fleshgordo/diskohedronled/pcb/screenshots/topmounting_revF.png

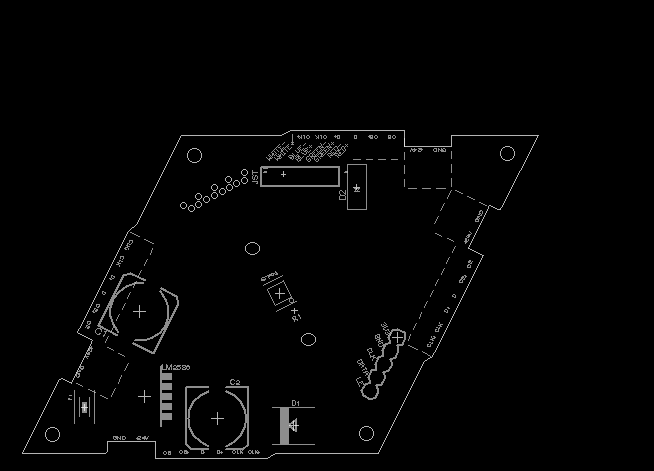
pcb/screenshots/topmounting_revF.png
