fleshgordo/diskohedronled/pcb/partlist/MountingBottomrevb.png

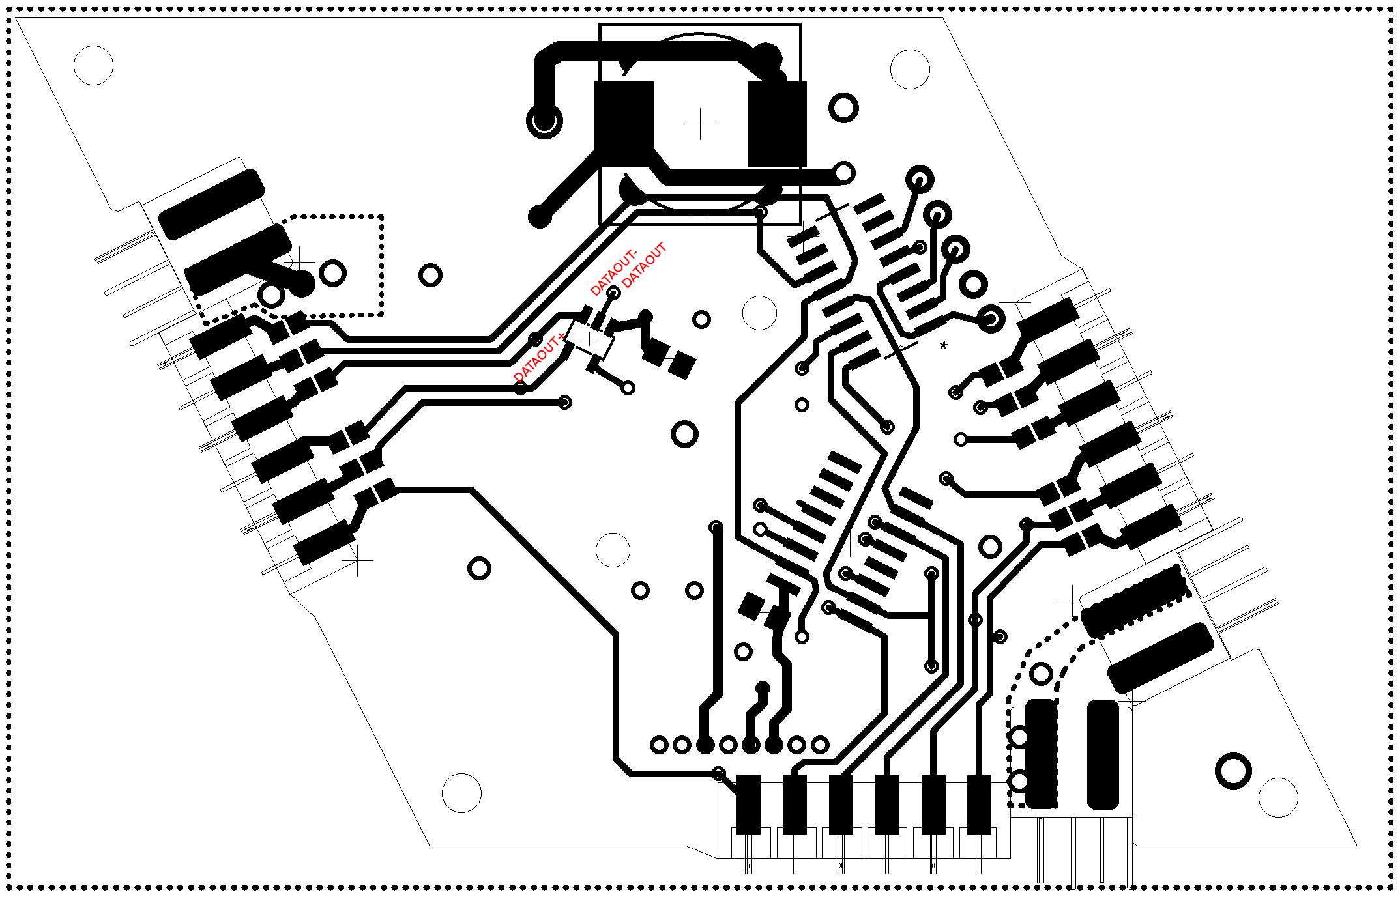
pcb/partlist/MountingBottomrevb.png
