fleshgordo/diskohedronled/pcb/partlist/MountingToprevc.png

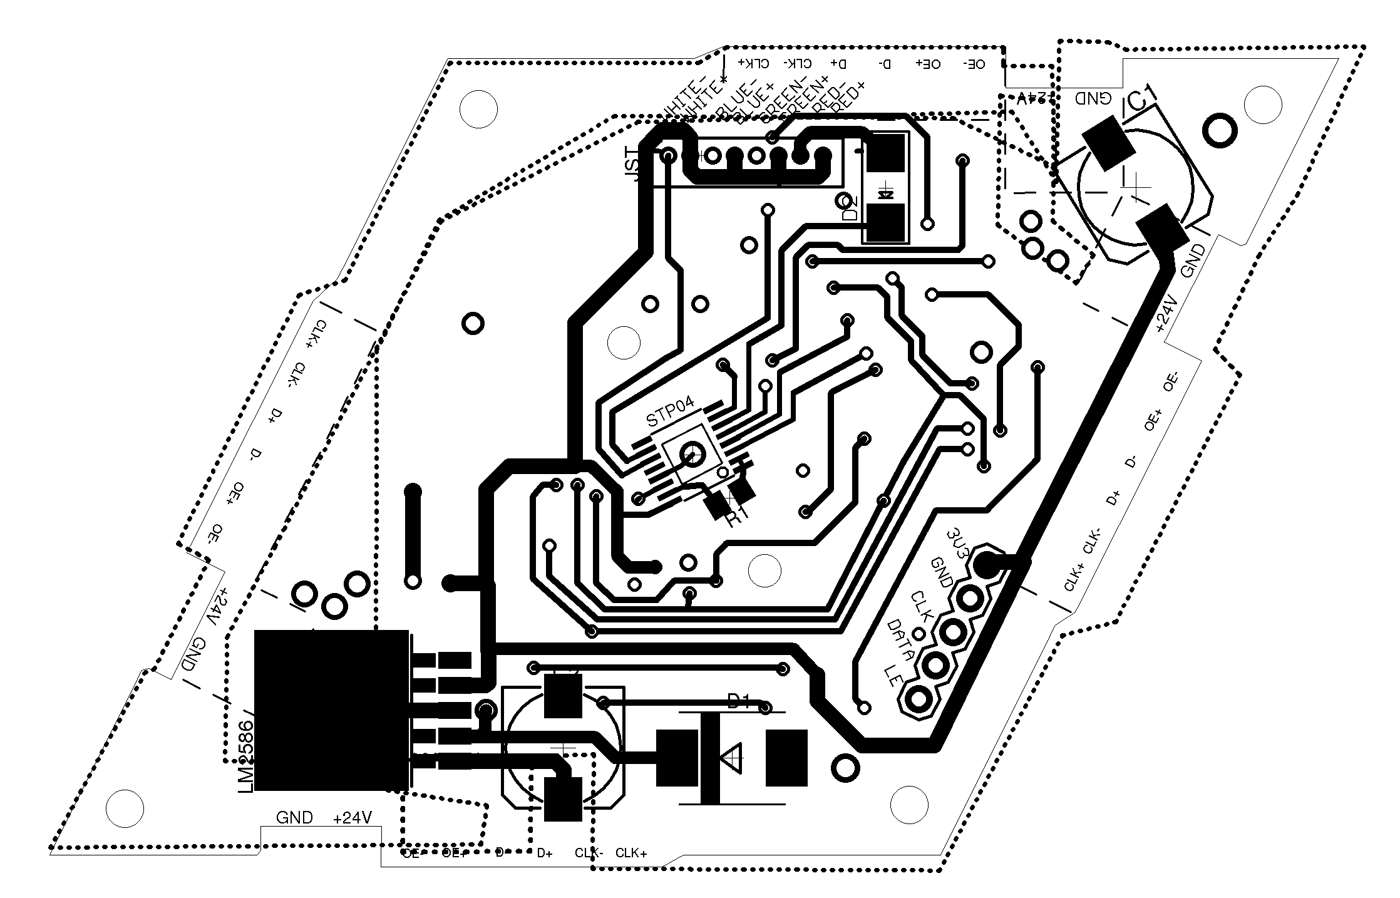
pcb/partlist/MountingToprevc.png
