fleshgordo/diskohedronled/construction/3dmodel/powerunit-box-revF.stl

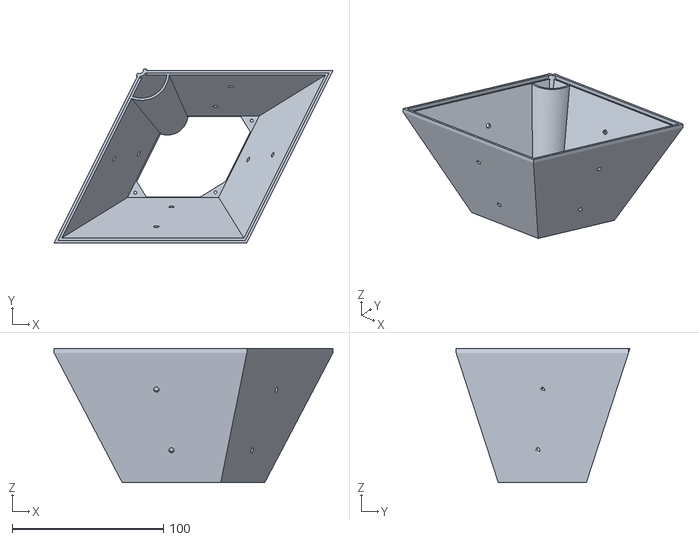
[picture p23: CAD file, 2015-05-11]
construction/3dmodel/powerunit-box-revF.stl
184.4 x 114.8 x 88.9
