fleshgordo/diskohedronled/construction/3dmodel/powerunit-triangle-revF-3rupe.stl

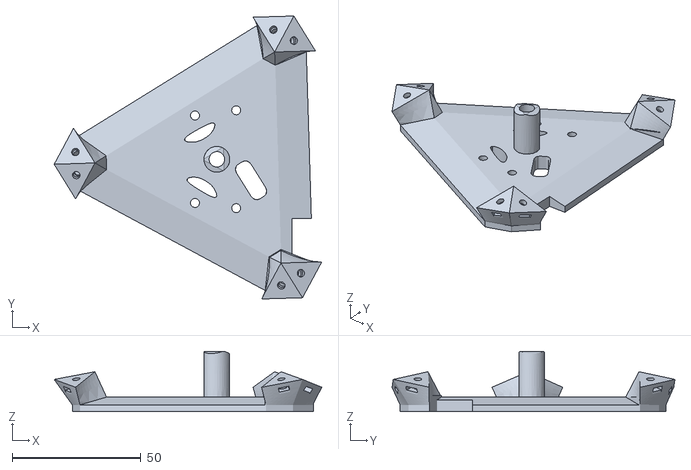
[picture p24: CAD file, 2015-05-11]
construction/3dmodel/powerunit-triangle-revF-3rupe.stl
104.0 x 109.9 x 23.5
