fleshgordo/diskohedronled/construction/3dmodel/powerunit-L-revF.stl

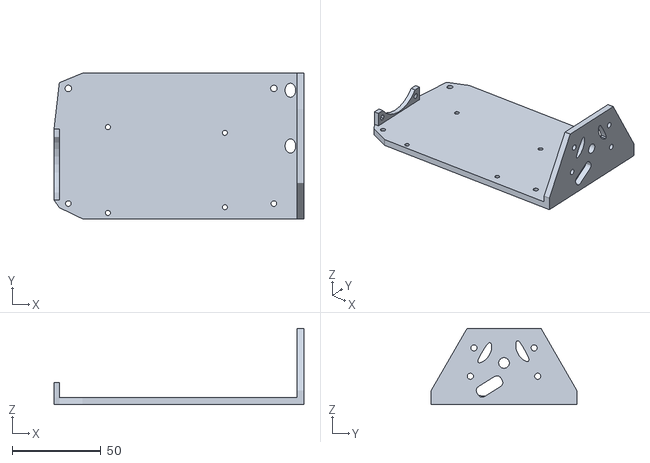
[picture p25: CAD file, 2015-05-11]
construction/3dmodel/powerunit-L-revF.stl
141.1 x 82.2 x 43.0
