fleshgordo/diskohedronled/construction/3dmodel/TeensyHolder108.stl

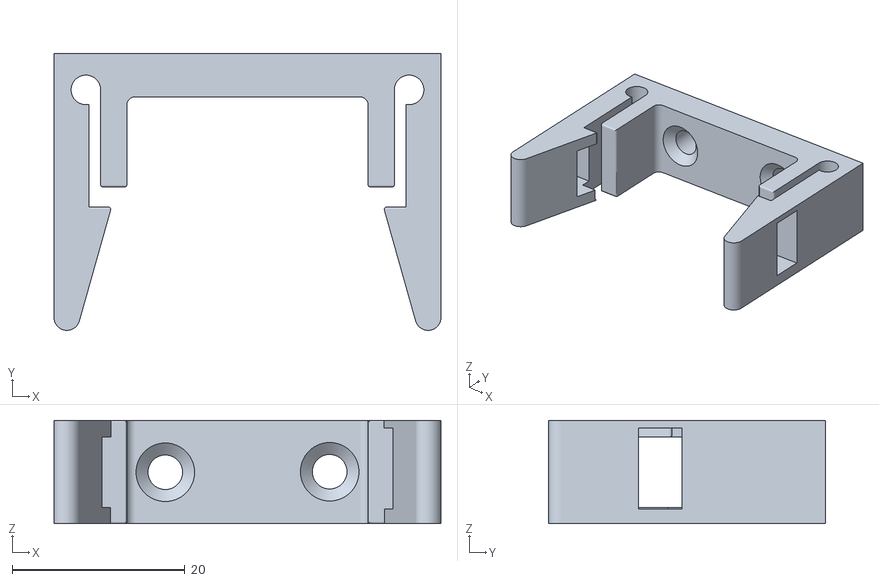
[picture p26: CAD file, 2015-05-11]
construction/3dmodel/TeensyHolder108.stl
44.9 x 32.1 x 12.0
