fleshgordo/diskohedronled/construction/3dmodel/piramida-revF-1-6-mesh.stl

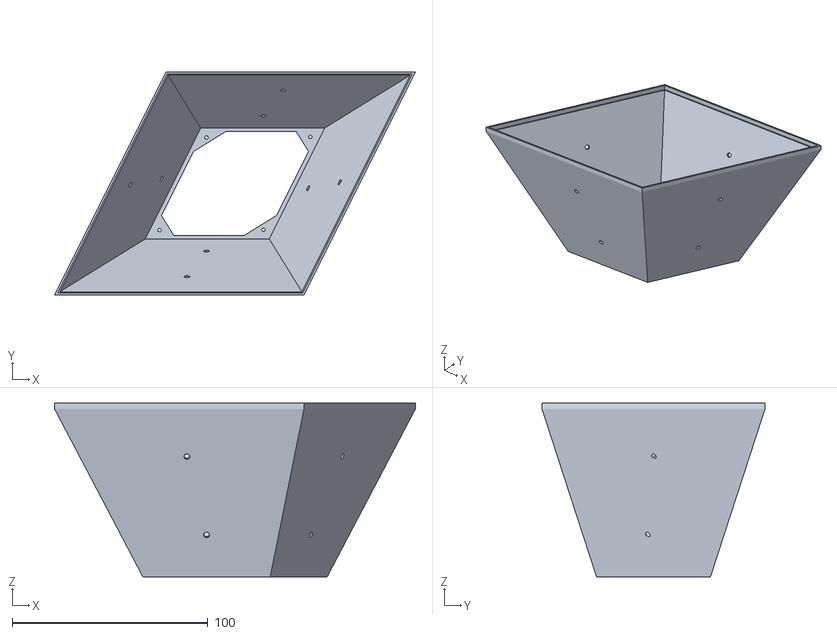
[picture p27: CAD file, 2015-03-30]
construction/3dmodel/piramida-revF-1-6-mesh.stl
184.4 x 113.9 x 88.9
