fleshgordo/diskohedronled/construction/3dmodel/piramida-revF.stl

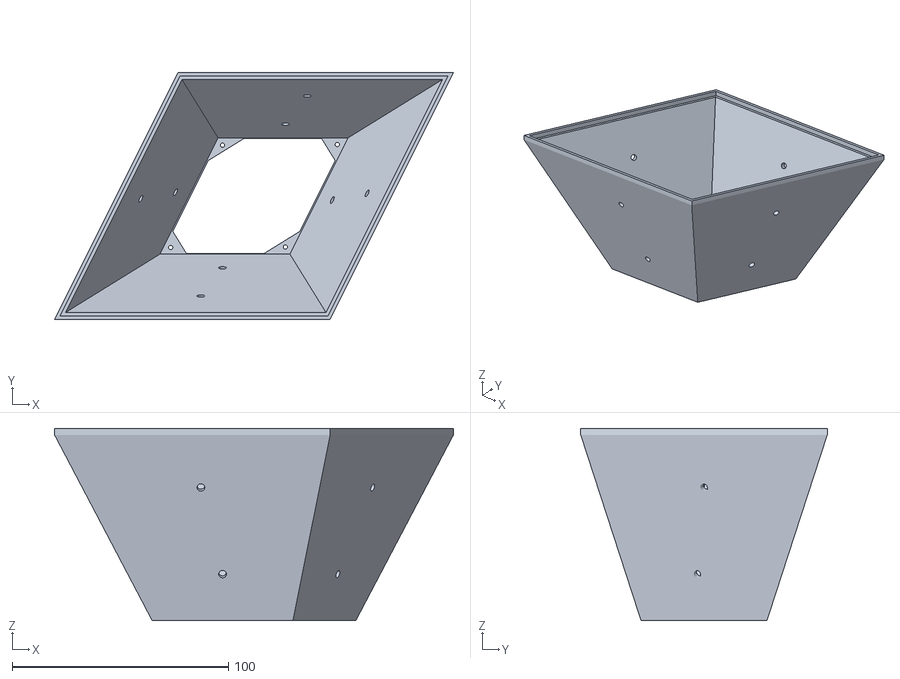
[picture p28: CAD file, 2015-03-30]
construction/3dmodel/piramida-revF.stl
184.4 x 113.9 x 88.9
