fleshgordo/diskohedronled/construction/3dmodel/powerunit-L-revB-3Dutility.stl

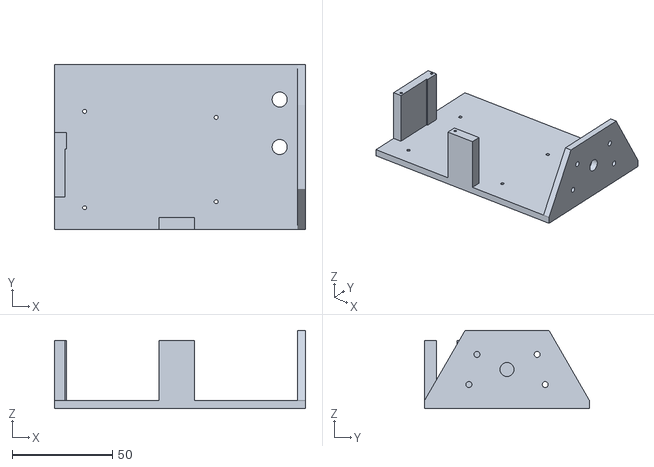
[picture p29: CAD file, 2015-03-28]
construction/3dmodel/powerunit-L-revB-3Dutility.stl
125.0 x 82.2 x 39.0
