fleshgordo/diskohedronled/construction/3dmodel/powerunit-triangle-revB-3Dutility.stl

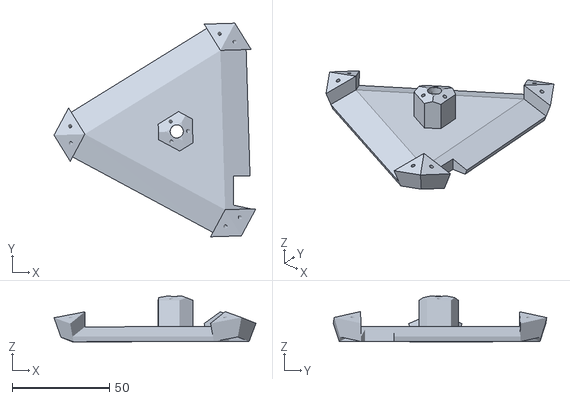
[picture p30: CAD file, 2015-03-28]
construction/3dmodel/powerunit-triangle-revB-3Dutility.stl
104.0 x 110.0 x 23.5
