fleshgordo/diskohedronled/construction/3dmodel/piramida-revB-2boxes-3Dutility.stl

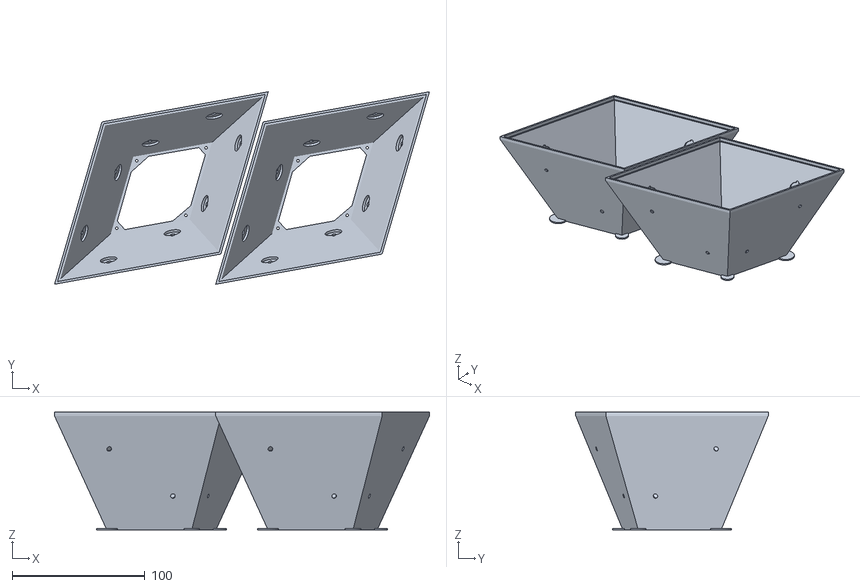
[picture p31: CAD file, 2014-12-30]
construction/3dmodel/piramida-revB-2boxes-3Dutility.stl
282.5 x 145.1 x 88.8
