fleshgordo/diskohedronled/construction/3dmodel/piramida-revB-3dutility.stl

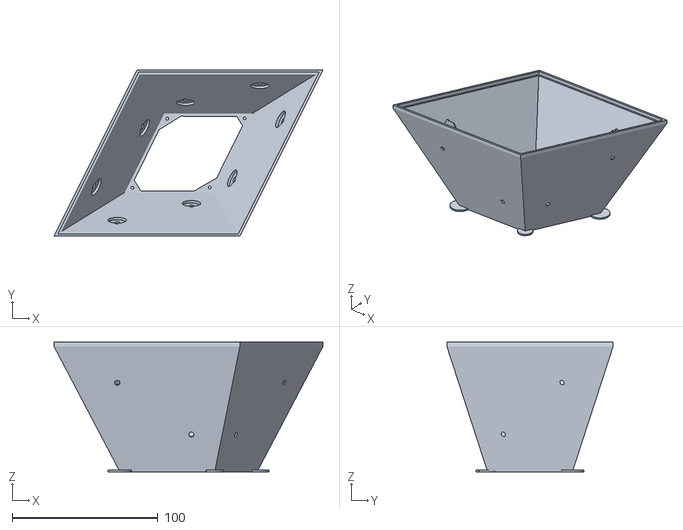
[picture p32: CAD file, 2014-12-30]
construction/3dmodel/piramida-revB-3dutility.stl
184.4 x 113.9 x 88.8
