fleshgordo/diskohedronled/construction/3dmodel/diskohedron4w_revc.dxf

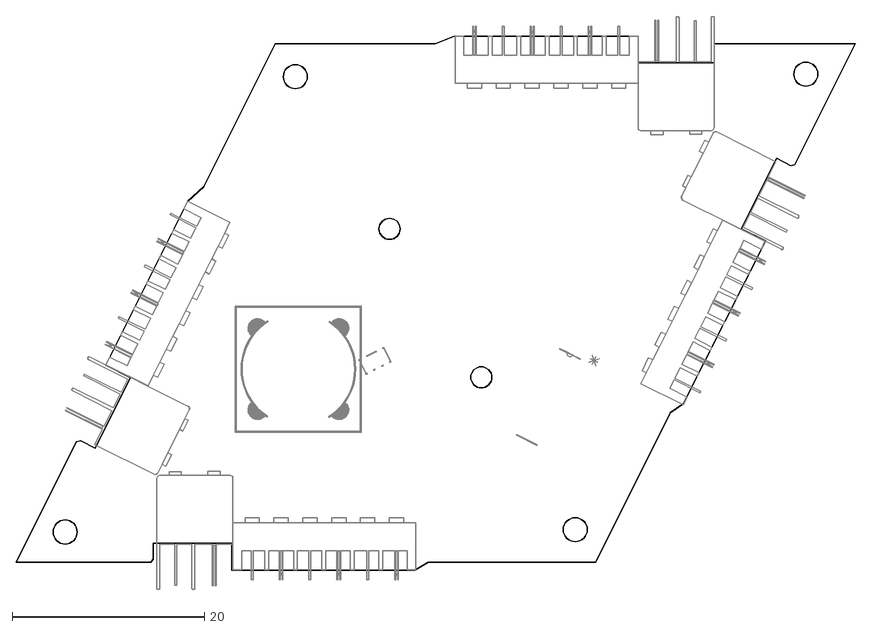
[picture p33: CAD file, 2014-07-10]
construction/3dmodel/diskohedron4w_revc.dxf
87.2 x 59.5
