fleshgordo/diskohedronled/construction/3dmodel/piramida-bb.stl

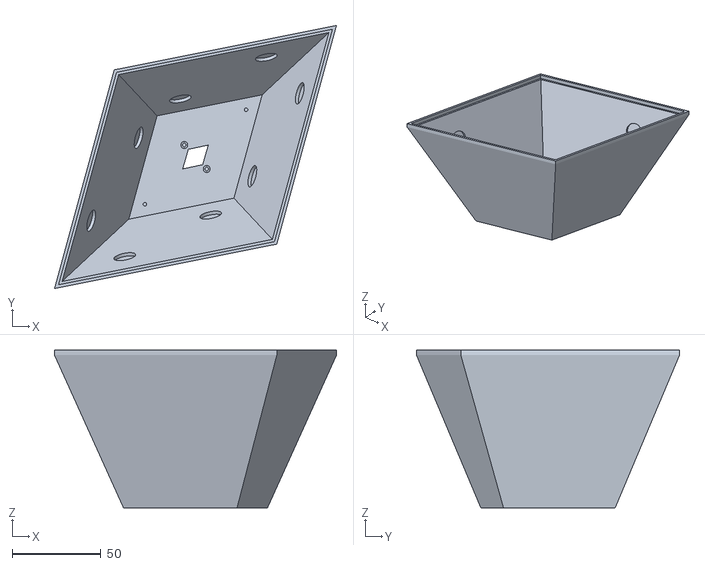
[picture p34: CAD file, 2014-05-03]
construction/3dmodel/piramida-bb.stl
158.5 x 147.8 x 88.8
