fleshgordo/diskohedronled/construction/3dmodel/visualization/inspector-kitty-op-art-casino.png

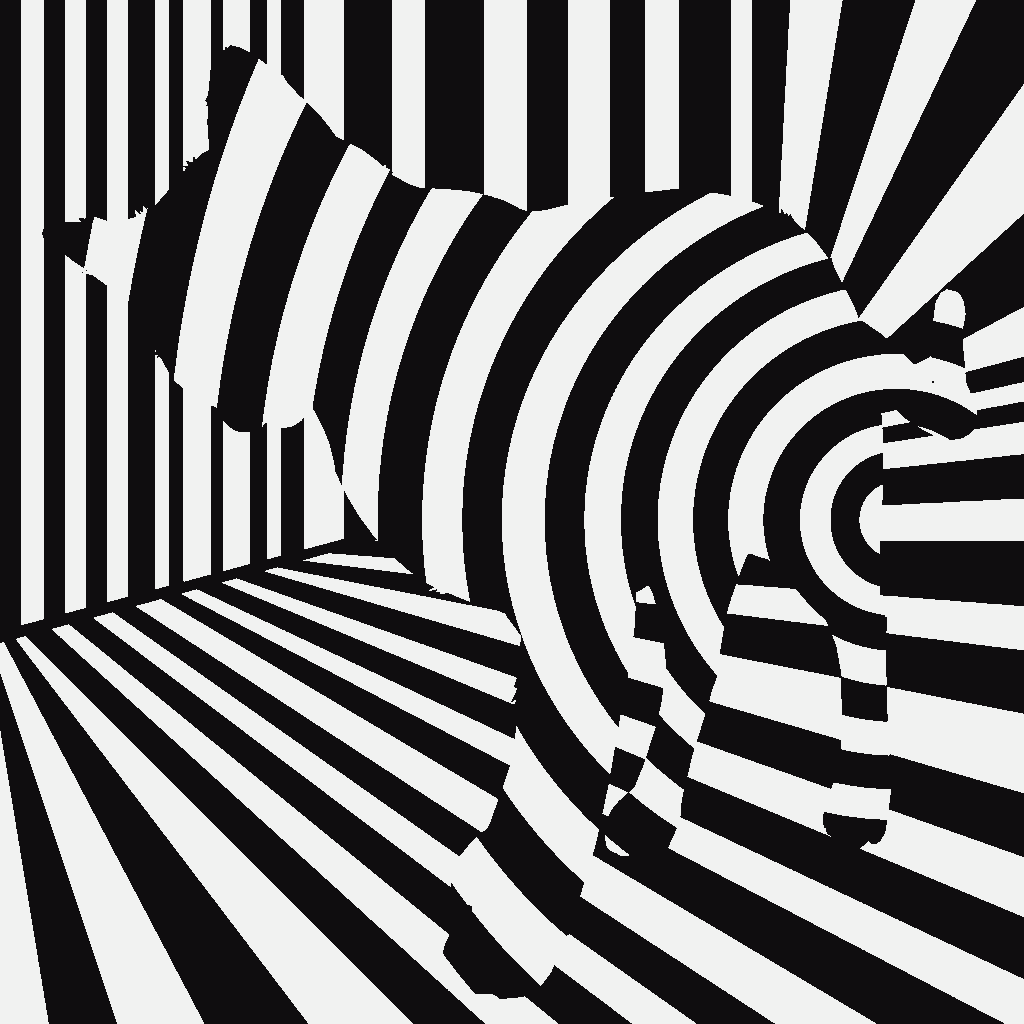
construction/3dmodel/visualization/inspector-kitty-op-art-casino.png
