fleshgordo/diskohedronled/construction/3dmodel/visualization/op-art-curved-necker-cubes.jpg

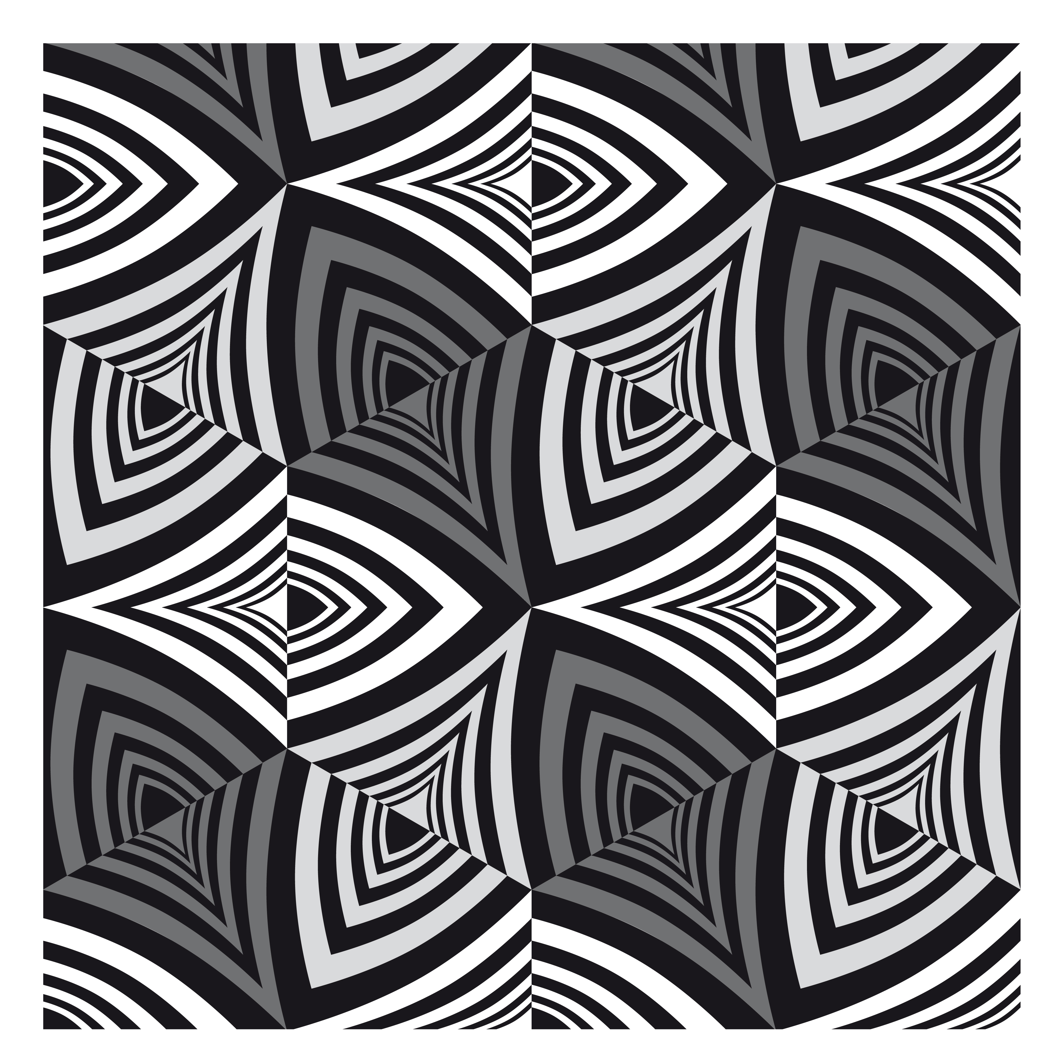
construction/3dmodel/visualization/op-art-curved-necker-cubes.jpg
