fleshgordo/diskohedronled/construction/3dmodel/visualization/op-art-sines.jpg

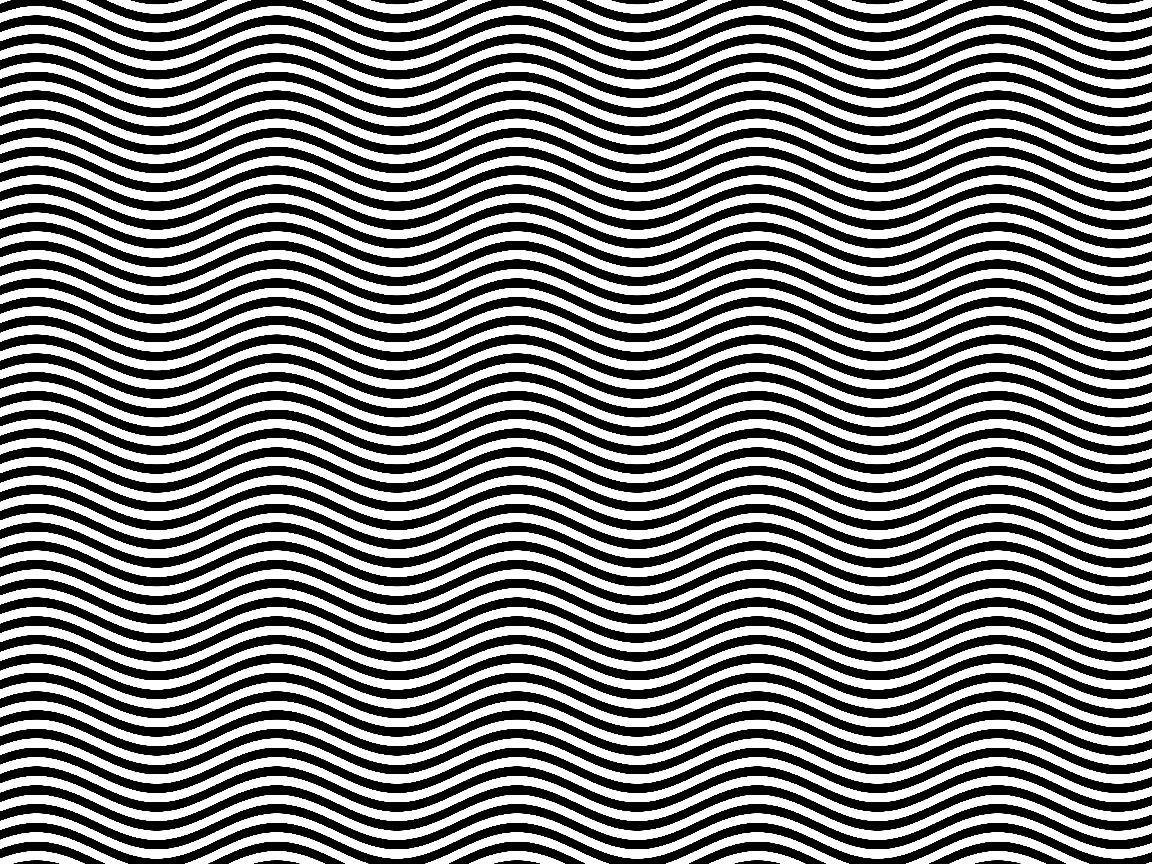
construction/3dmodel/visualization/op-art-sines.jpg
