fleshgordo/diskohedronled/construction/3dmodel/visualization/render-rgb-02.jpg

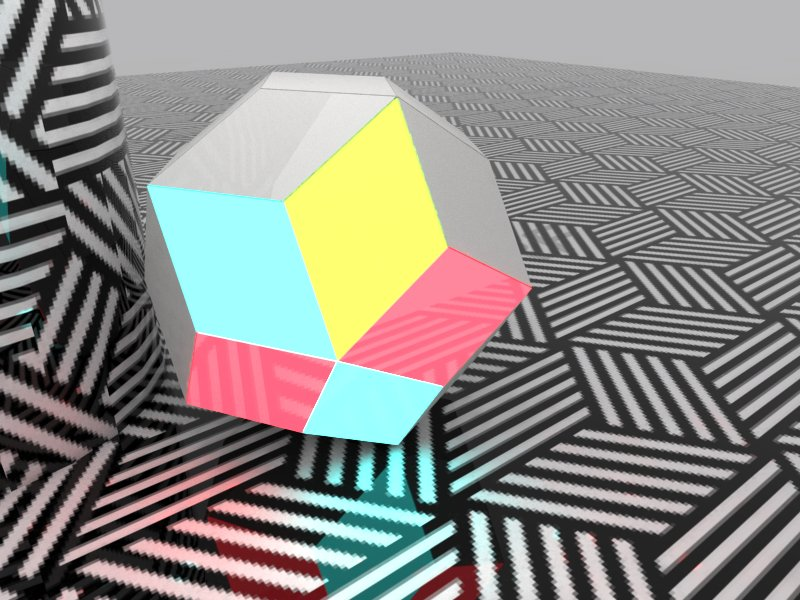
construction/3dmodel/visualization/render-rgb-02.jpg
