fleshgordo/diskohedronled/pcb/assembly/instruction_hermaphrodit.jpg

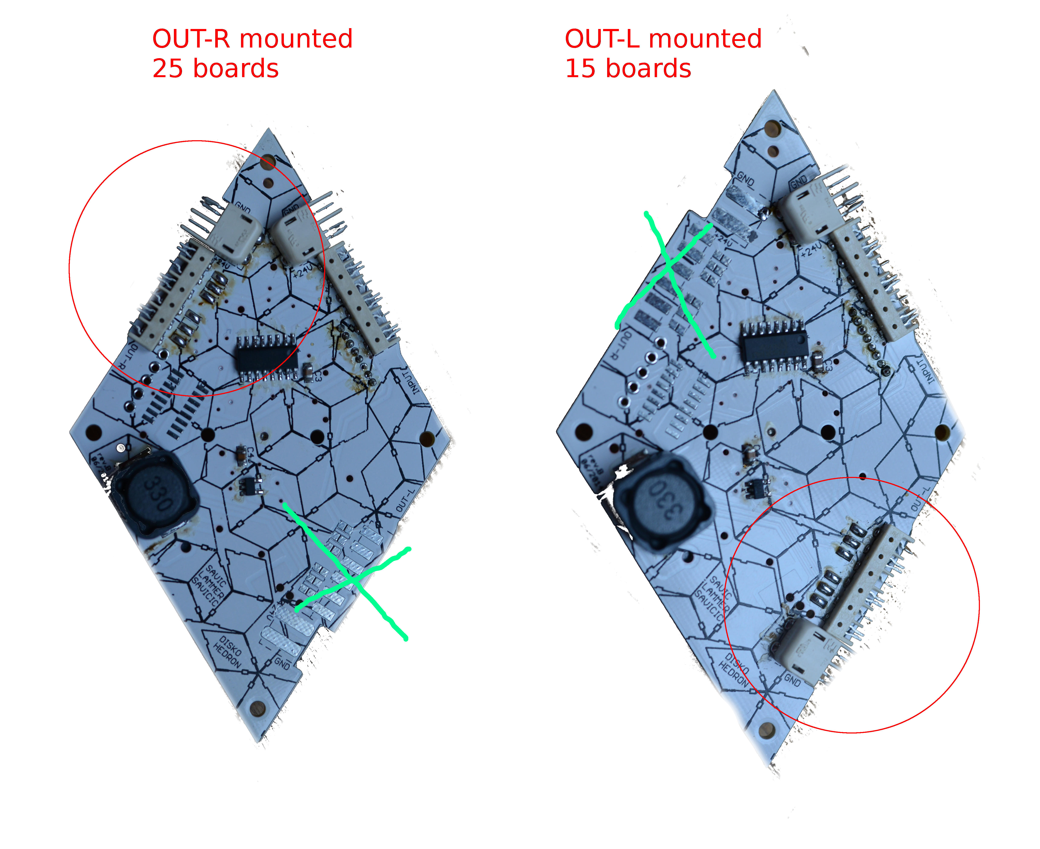
pcb/assembly/instruction_hermaphrodit.jpg
