fleshgordo/diskohedronled/pcb/assembly/revF_mounting_bottom.png

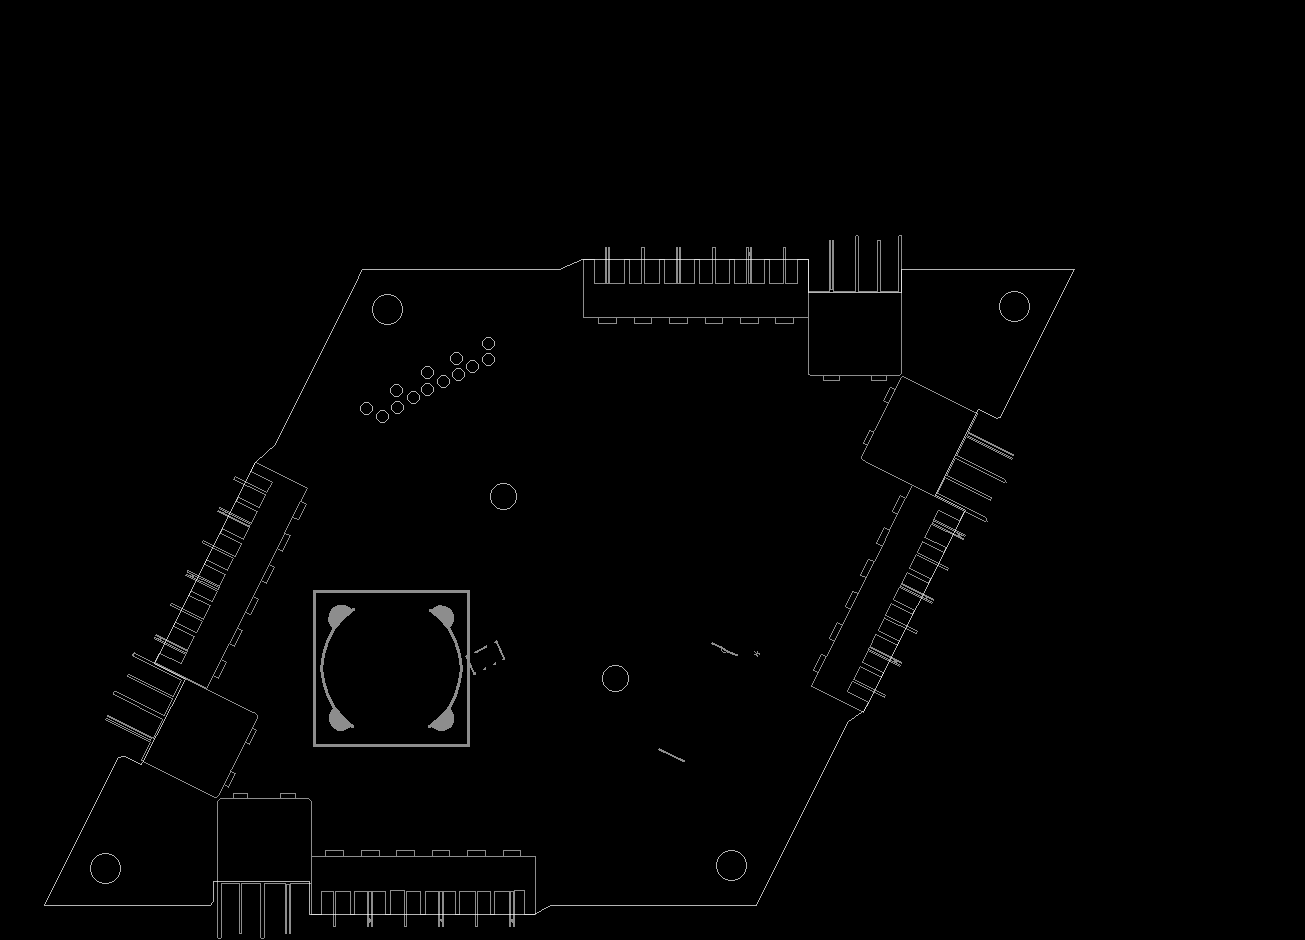
pcb/assembly/revF_mounting_bottom.png
